TheSinc/BadmintonAce/Ace D4/CAD/ACE D4 WHEEL REV 0.STEP

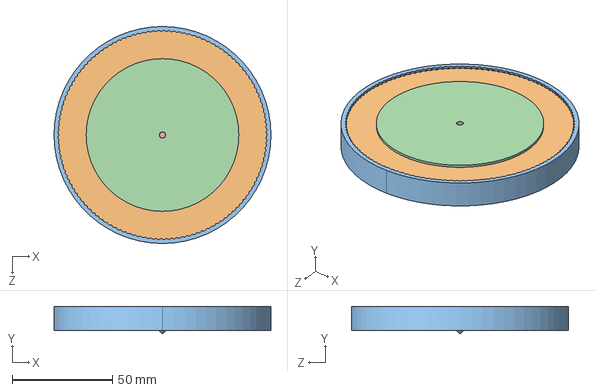
[picture p15: CAD file, 2023-09-12]
Ace D4/CAD/ACE D4 WHEEL REV 0.STEP
108.0 x 13.6 x 108.0 mm
