TheSinc/BadmintonAce/Ace D4/CAD/ACE D4 MOTOR MOUNT REV 0.STEP

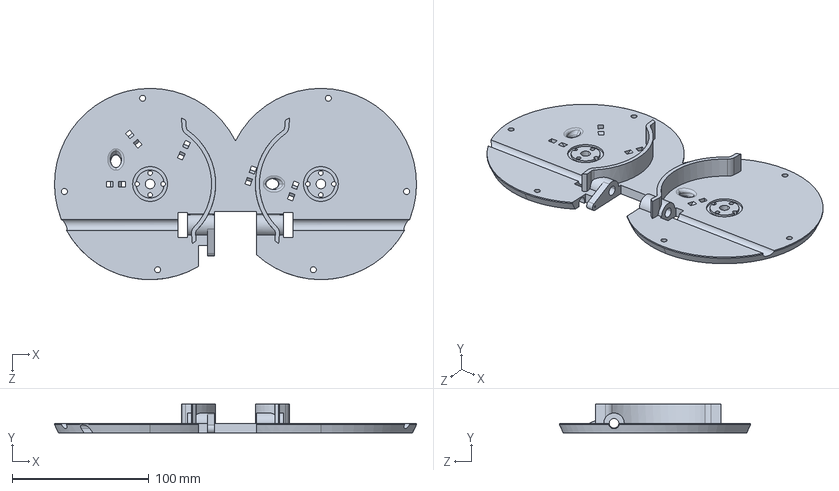
[picture p16: CAD file, 2023-09-12]
Ace D4/CAD/ACE D4 MOTOR MOUNT REV 0.STEP
265.0 x 21.0 x 140.0 mm
